lukacslacko/puzzle/438k.dxf

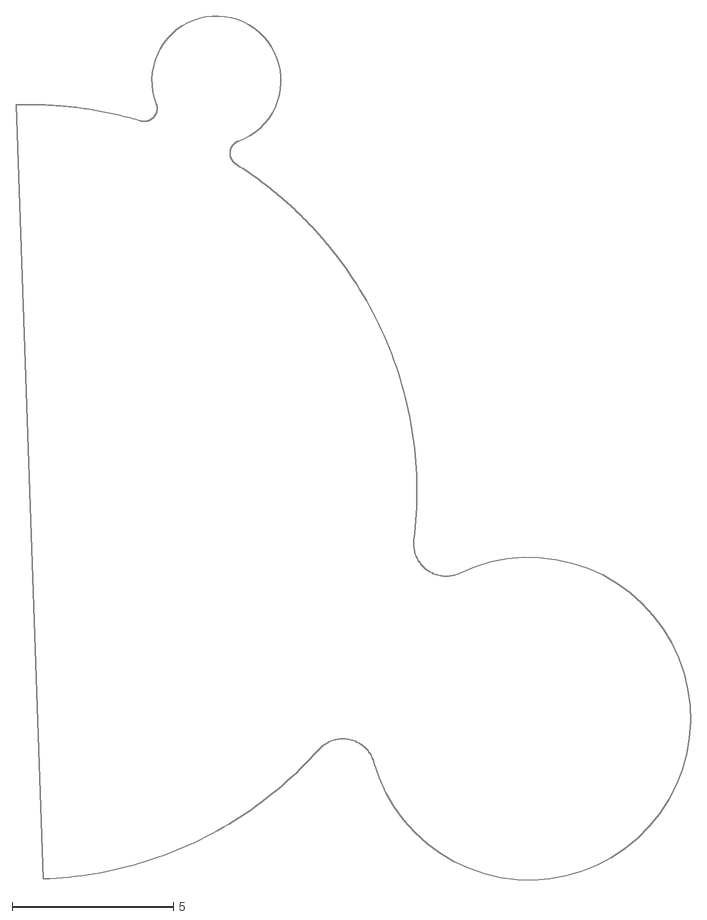
[picture p4: CAD file, 2023-12-27]
438k.dxf
20.9 x 26.8
