lukacslacko/puzzle/438l.dxf

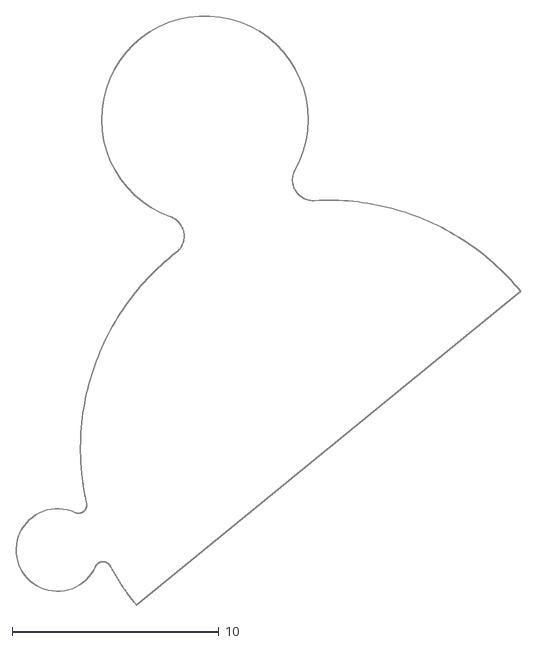
[picture p5: CAD file, 2023-12-27]
438l.dxf
24.4 x 28.5
