lukacslacko/puzzle/438c.dxf

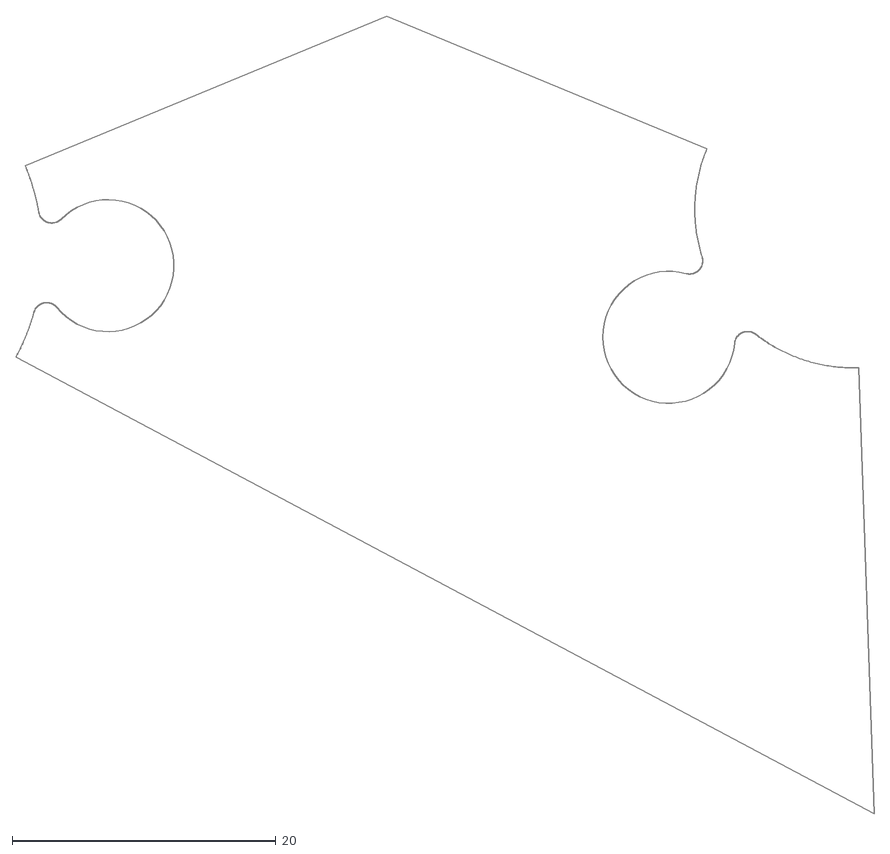
[picture p6: CAD file, 2023-12-27]
438c.dxf
65.0 x 60.4
