lukacslacko/puzzle/438j.dxf

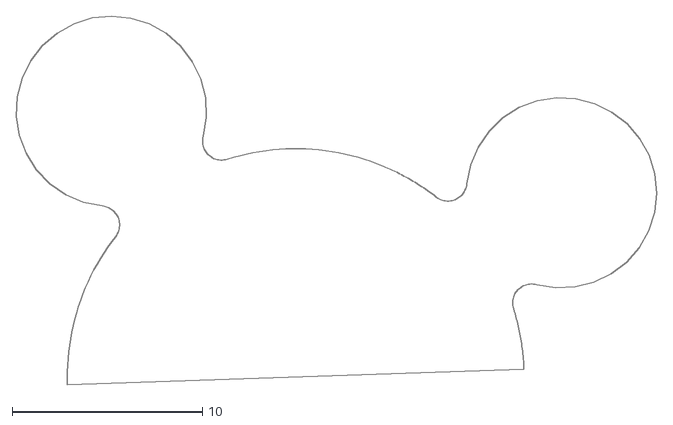
[picture p7: CAD file, 2023-12-27]
438j.dxf
33.6 x 19.4
