lukacslacko/puzzle/438m.dxf

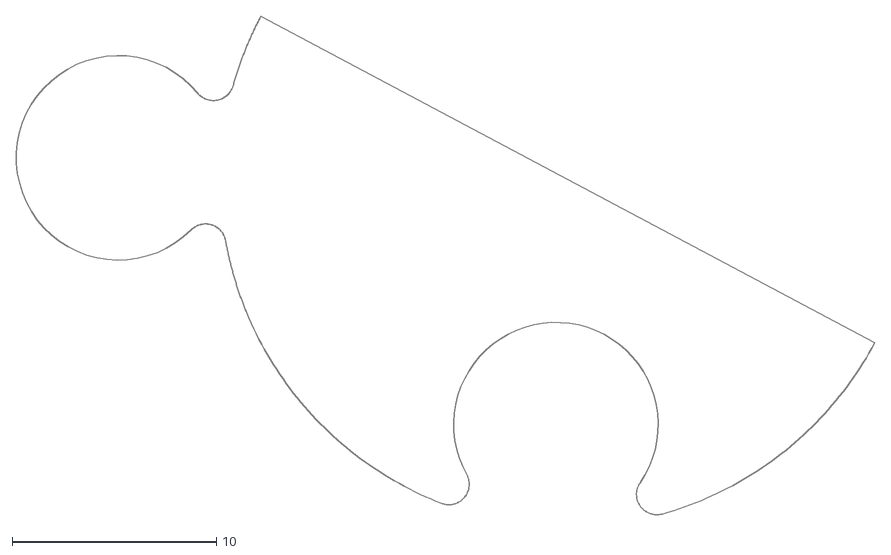
[picture p8: CAD file, 2023-12-27]
438m.dxf
42.0 x 24.4
