lukacslacko/puzzle/simple-sq-3-8-7.dxf

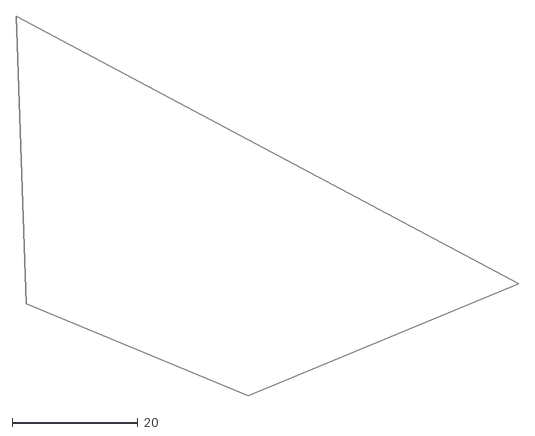
[picture p9: CAD file, 2023-12-27]
simple-sq-3-8-7.dxf
80.0 x 60.4
