lukacslacko/puzzle/simple-sq-3-8-3.dxf

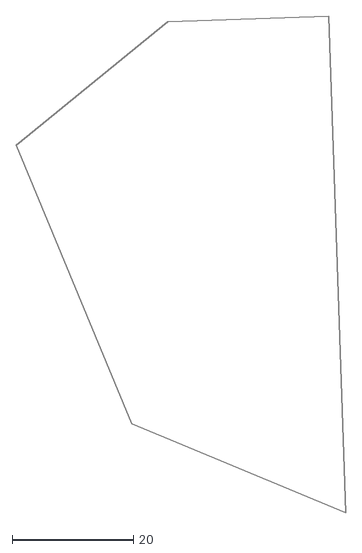
[picture p10: CAD file, 2023-12-27]
simple-sq-3-8-3.dxf
54.4 x 81.9
