lukacslacko/puzzle/simple-sq-3-8-1.dxf

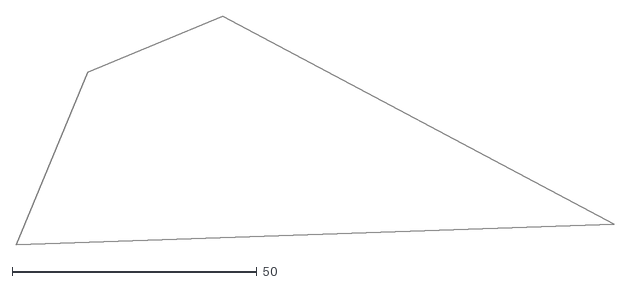
[picture p11: CAD file, 2023-12-27]
simple-sq-3-8-1.dxf
122.3 x 46.8
