lukacslacko/puzzle/438a.dxf

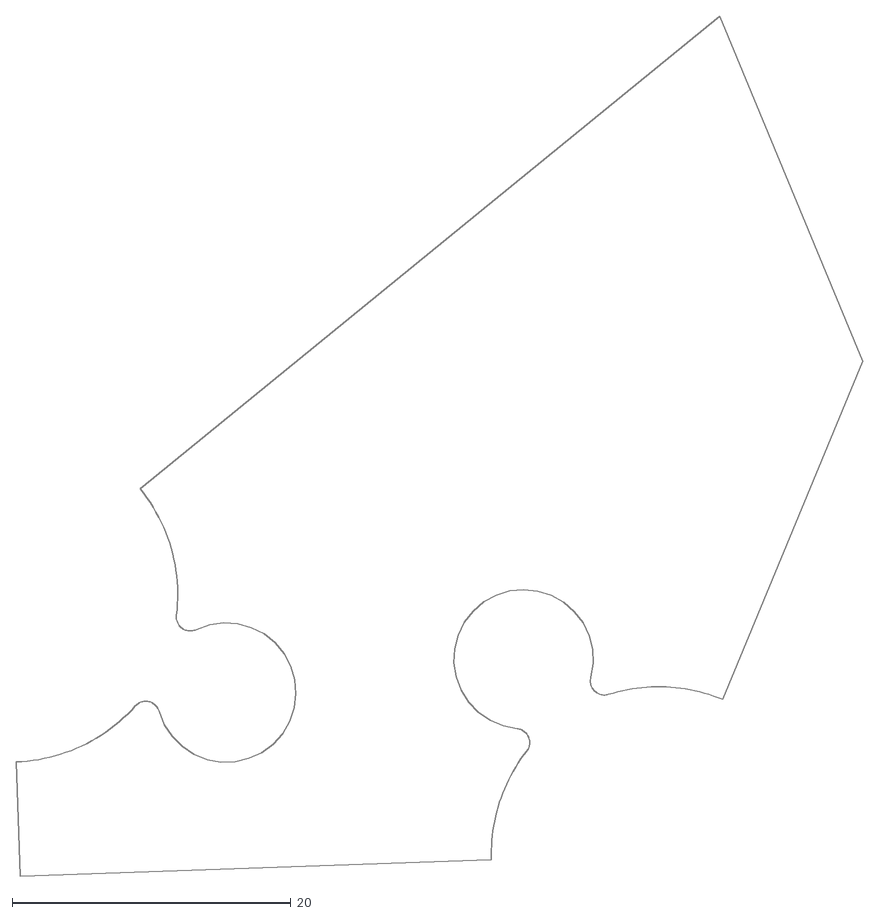
[picture p12: CAD file, 2023-12-27]
438a.dxf
60.7 x 61.7
