lukacslacko/puzzle/438d.dxf

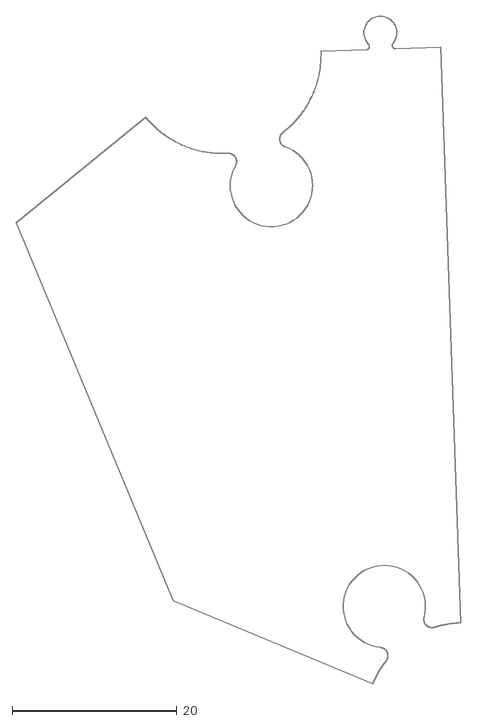
[picture p13: CAD file, 2023-12-27]
438d.dxf
54.0 x 81.1
