lukacslacko/puzzle/simple-sq-3-8-0.dxf

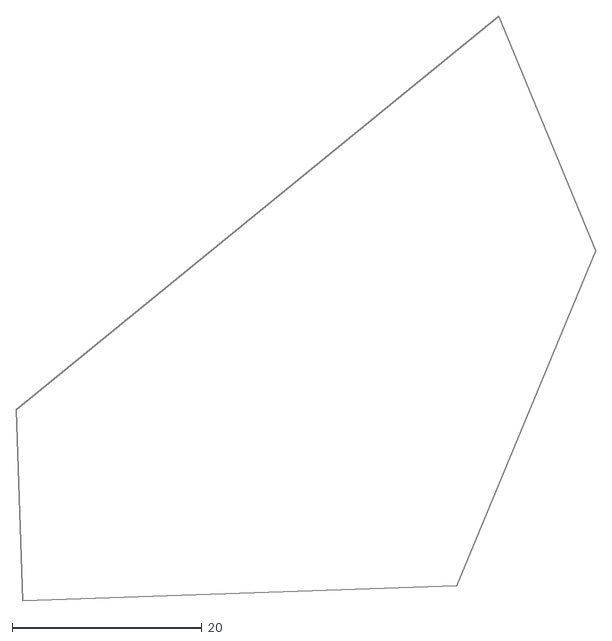
[picture p14: CAD file, 2023-12-27]
simple-sq-3-8-0.dxf
61.1 x 61.7
