lukacslacko/puzzle/438g.dxf

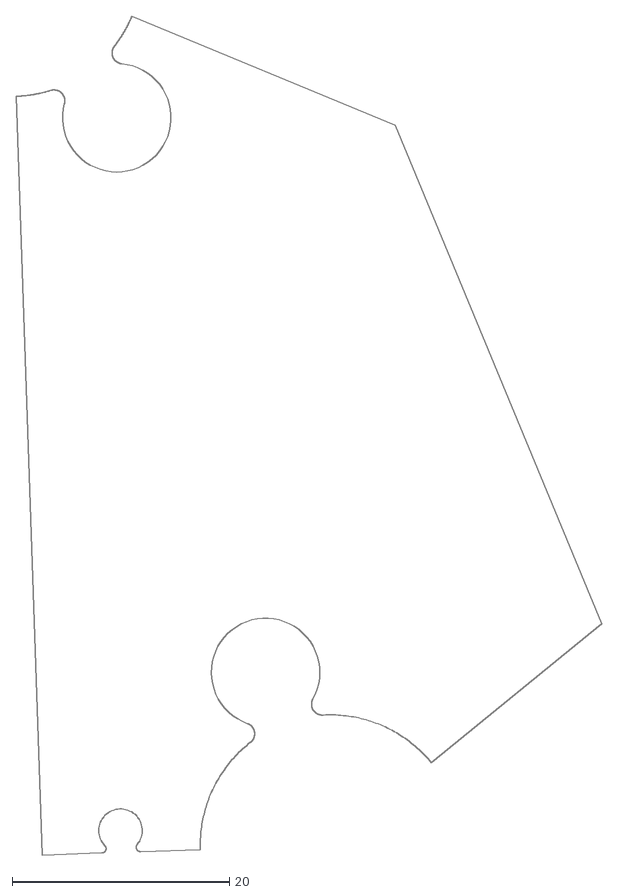
[picture p15: CAD file, 2023-12-27]
438g.dxf
54.0 x 77.3
