lukacslacko/puzzle/simple-sq-3-8-4.dxf

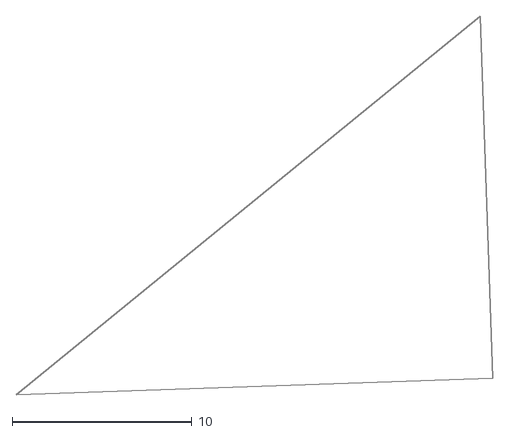
[picture p16: CAD file, 2023-12-27]
simple-sq-3-8-4.dxf
26.6 x 21.1
