lukacslacko/puzzle/438e.dxf

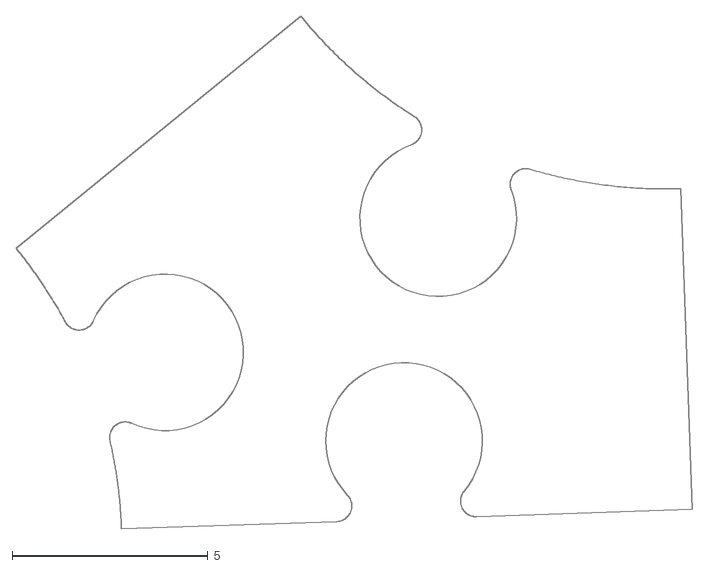
[picture p17: CAD file, 2023-12-27]
438e.dxf
17.3 x 13.1
