lukacslacko/puzzle/438i.dxf

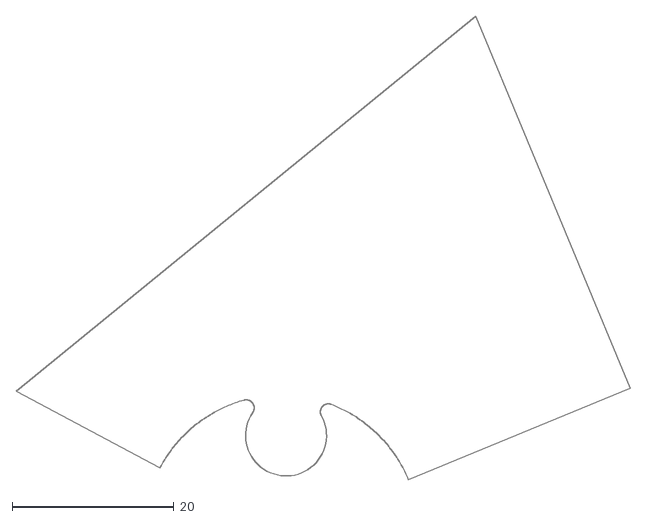
[picture p18: CAD file, 2023-12-27]
438i.dxf
75.9 x 57.3
