lukacslacko/puzzle/simple-sq-3-8-5.dxf

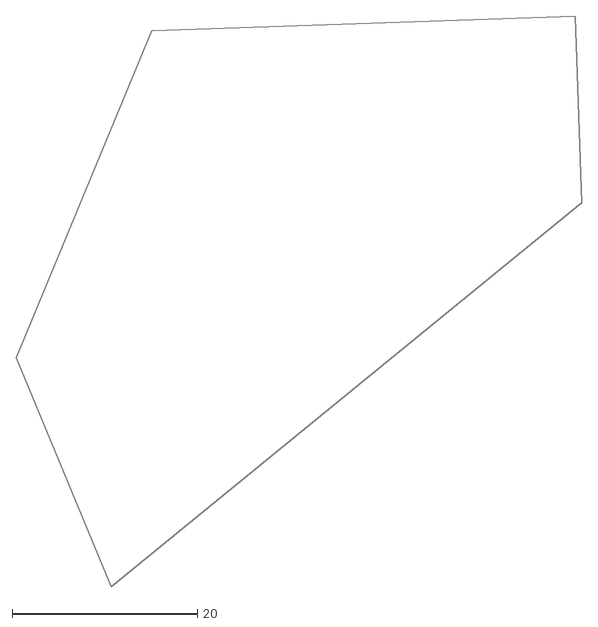
[picture p19: CAD file, 2023-12-27]
simple-sq-3-8-5.dxf
61.1 x 61.7
