lukacslacko/puzzle/simple-sq-3-8-9.dxf

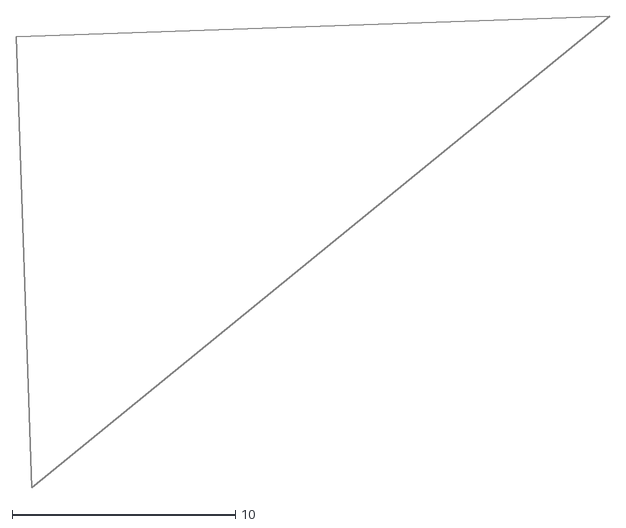
[picture p20: CAD file, 2023-12-27]
simple-sq-3-8-9.dxf
26.6 x 21.1
