lukacslacko/puzzle/simple-sq-3-8-8.dxf

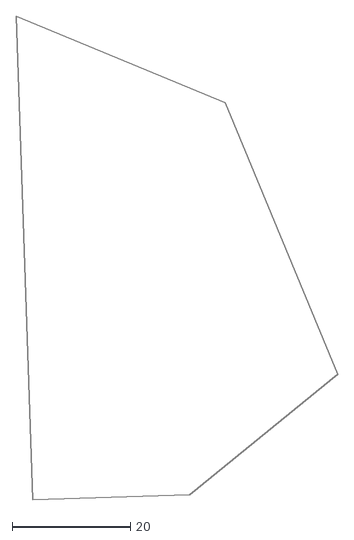
[picture p21: CAD file, 2023-12-27]
simple-sq-3-8-8.dxf
54.4 x 81.9
