lukacslacko/puzzle/simple-sq-3-8-12.dxf

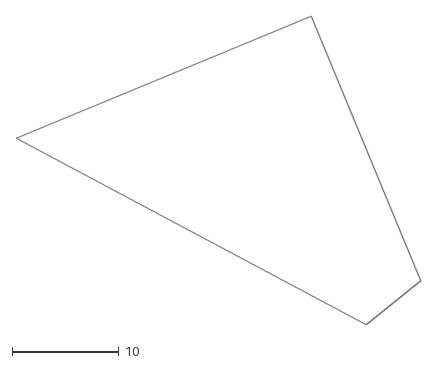
[picture p22: CAD file, 2023-12-27]
simple-sq-3-8-12.dxf
37.9 x 28.9
