lukacslacko/puzzle/simple-sq-3-8-11.dxf

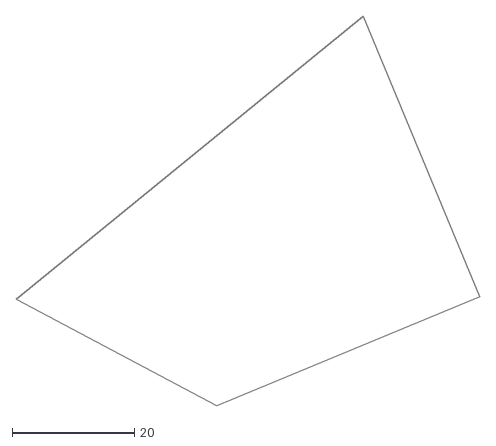
[picture p23: CAD file, 2023-12-27]
simple-sq-3-8-11.dxf
75.9 x 63.8
