lukacslacko/puzzle/simple-sq-3-8-13.dxf

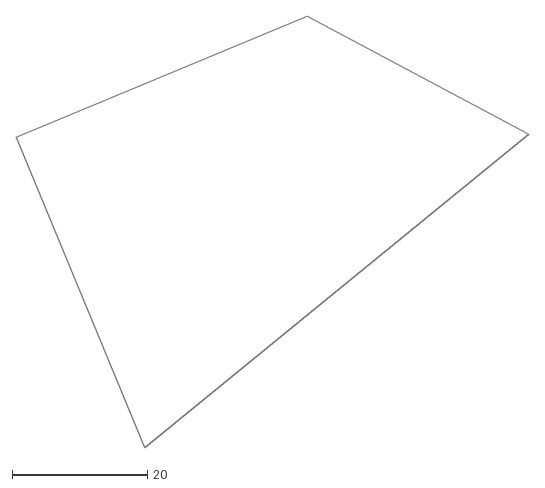
[picture p24: CAD file, 2023-12-27]
simple-sq-3-8-13.dxf
75.9 x 63.8
