lukacslacko/puzzle/simple-sq-3-8-6.dxf

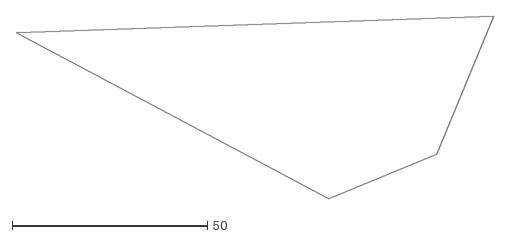
[picture p25: CAD file, 2023-12-27]
simple-sq-3-8-6.dxf
122.3 x 46.8
