lukacslacko/puzzle/simple-sq-3-8-2.dxf

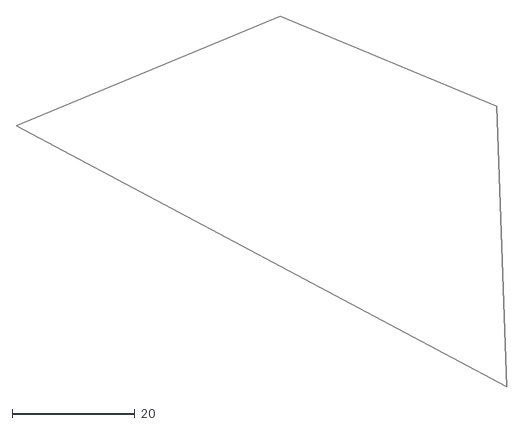
[picture p26: CAD file, 2023-12-27]
simple-sq-3-8-2.dxf
80.0 x 60.4
