lukacslacko/puzzle/438b.dxf

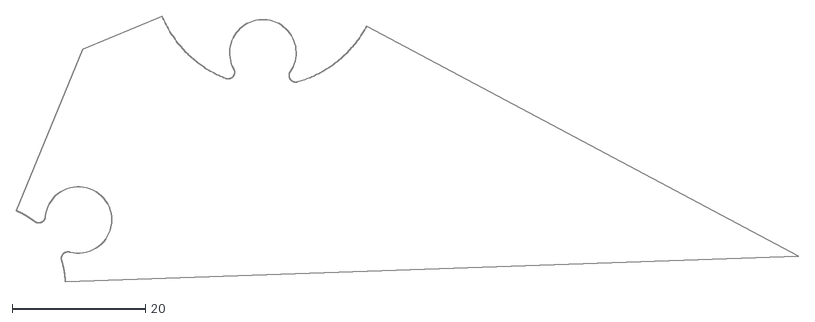
[picture p27: CAD file, 2023-12-27]
438b.dxf
117.7 x 39.9
