lukacslacko/puzzle/438f.dxf

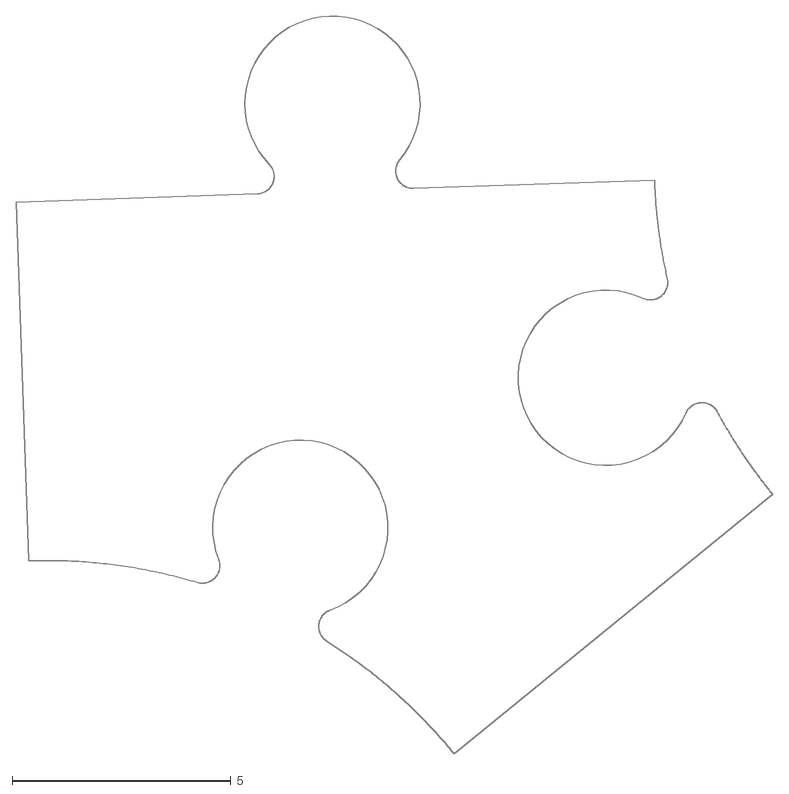
[picture p28: CAD file, 2023-12-27]
438f.dxf
17.3 x 16.8
