lukacslacko/puzzle/simple-sq-3-8-10.dxf

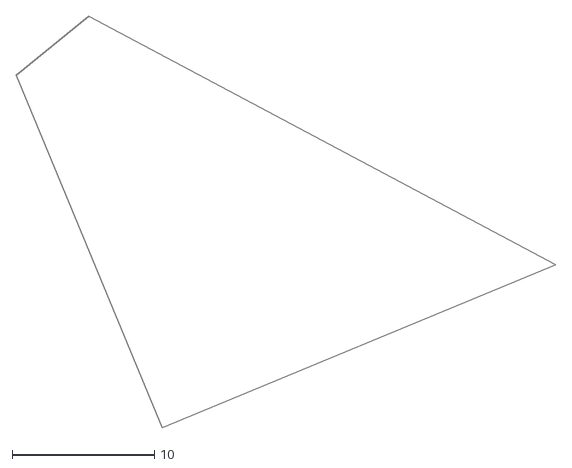
[picture p29: CAD file, 2023-12-27]
simple-sq-3-8-10.dxf
37.9 x 28.9
