lukacslacko/puzzle/438h.dxf

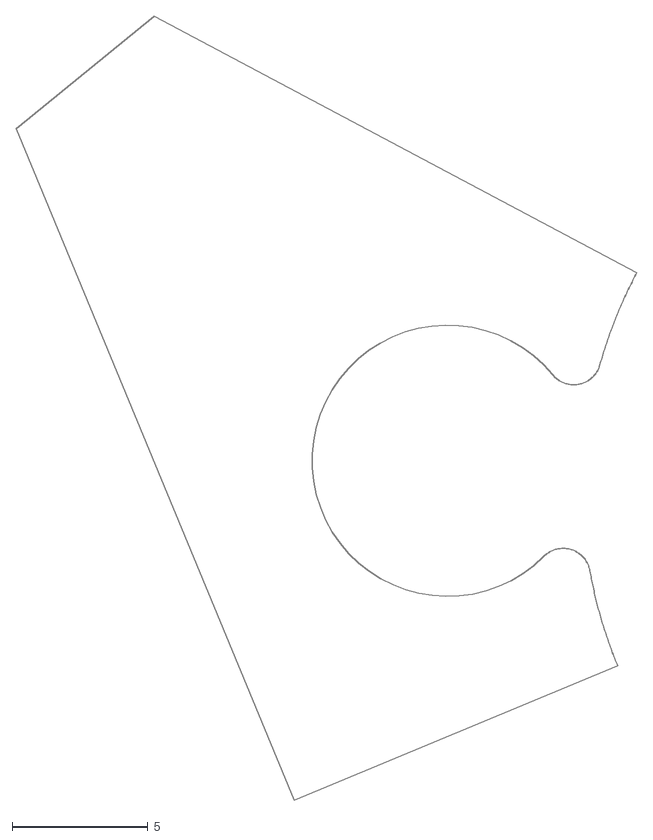
[picture p30: CAD file, 2023-12-27]
438h.dxf
22.9 x 28.9
