lukacslacko/puzzle/sq-3-8-a.dxf

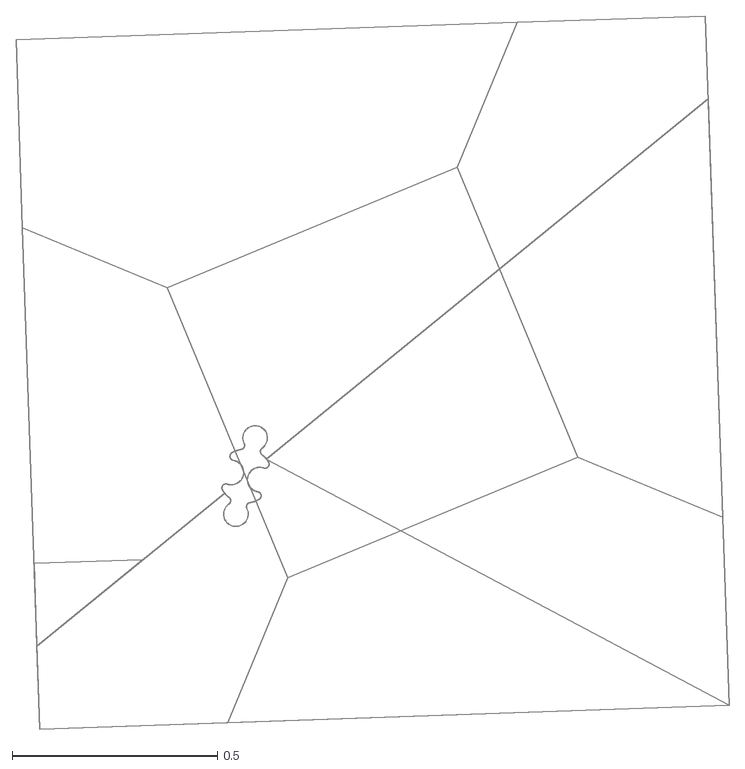
[picture p31: CAD file, 2023-12-26]
sq-3-8-a.dxf
1.74 x 1.74
