lukacslacko/puzzle/sq-3-8-b.dxf

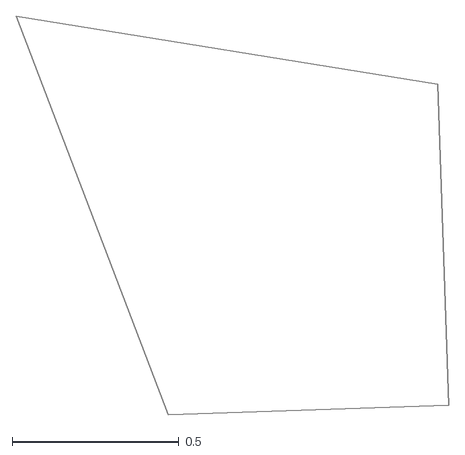
[picture p32: CAD file, 2023-12-26]
sq-3-8-b.dxf
1.29 x 1.19
