lukacslacko/puzzle/sq-tree-g.dxf

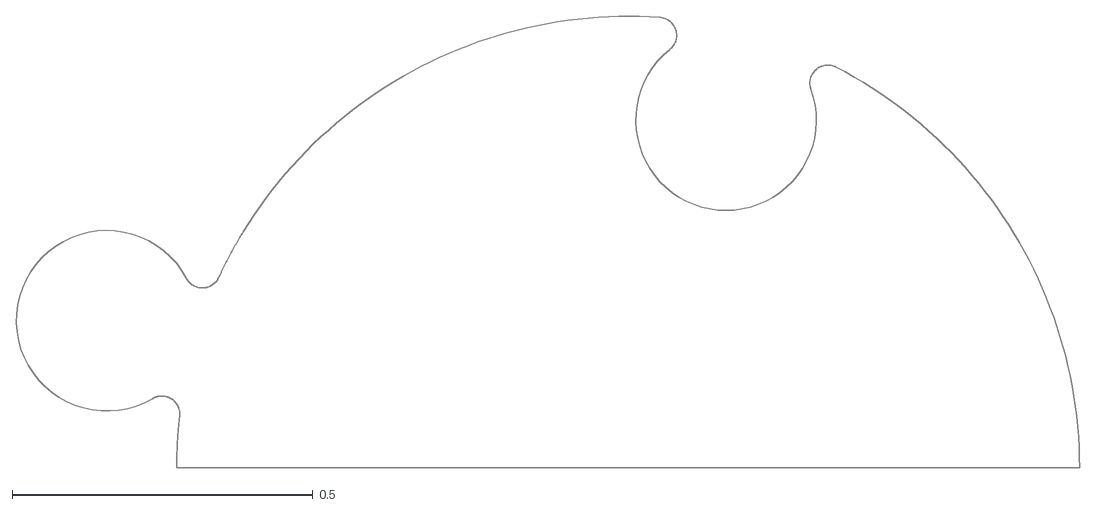
[picture p33: CAD file, 2023-12-25]
sq-tree-g.dxf
1.77 x 0.75
