lukacslacko/puzzle/sq-tree-b.dxf

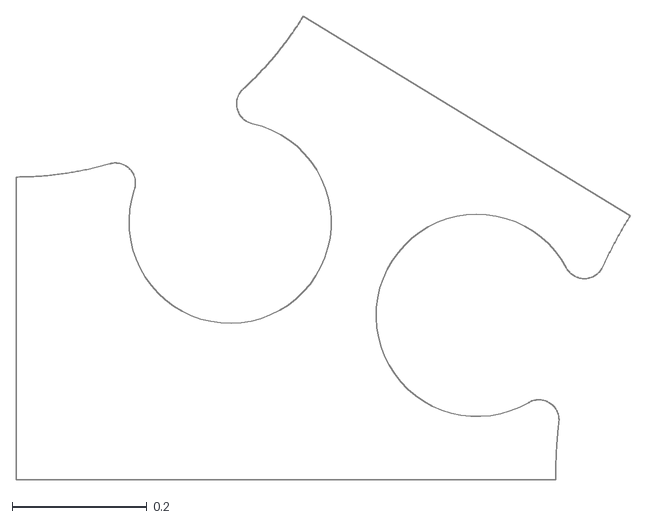
[picture p34: CAD file, 2023-12-25]
sq-tree-b.dxf
0.911 x 0.688
