lukacslacko/puzzle/sq-tree-d.dxf

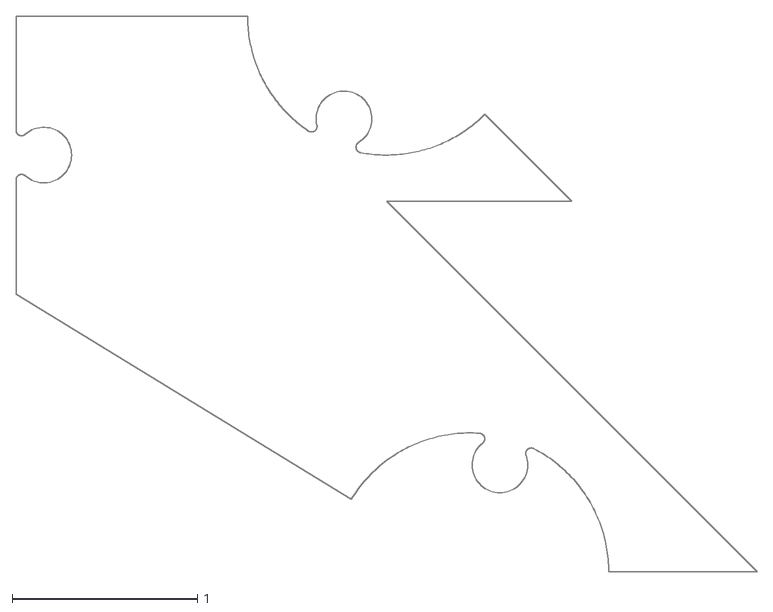
[picture p35: CAD file, 2023-12-25]
sq-tree-d.dxf
4.00 x 3.00
