lukacslacko/puzzle/sq-tree-f.dxf

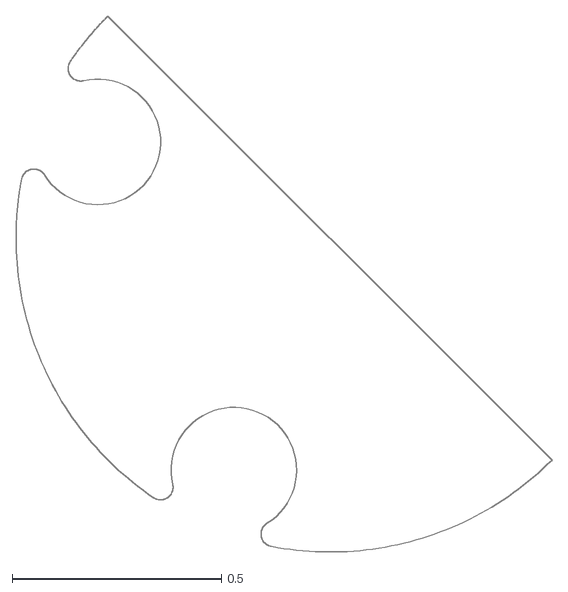
[picture p36: CAD file, 2023-12-25]
sq-tree-f.dxf
1.28 x 1.28
