lukacslacko/puzzle/linear_tab.dxf

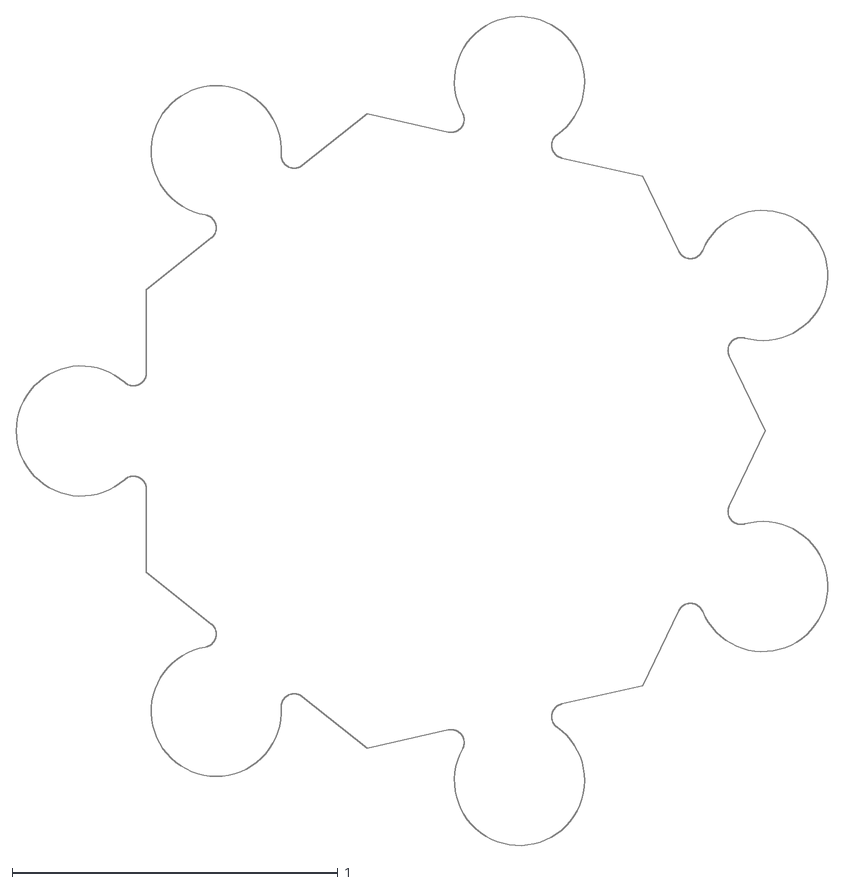
[picture p37: CAD file, 2023-12-25]
linear_tab.dxf
2.49 x 2.55
