lukacslacko/puzzle/sq-tree-a2.dxf

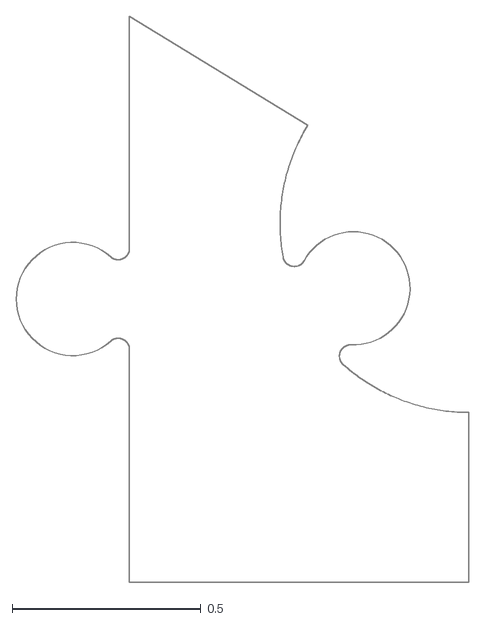
[picture p38: CAD file, 2023-12-25]
sq-tree-a2.dxf
1.20 x 1.50
