lukacslacko/puzzle/sq-tree-e.dxf

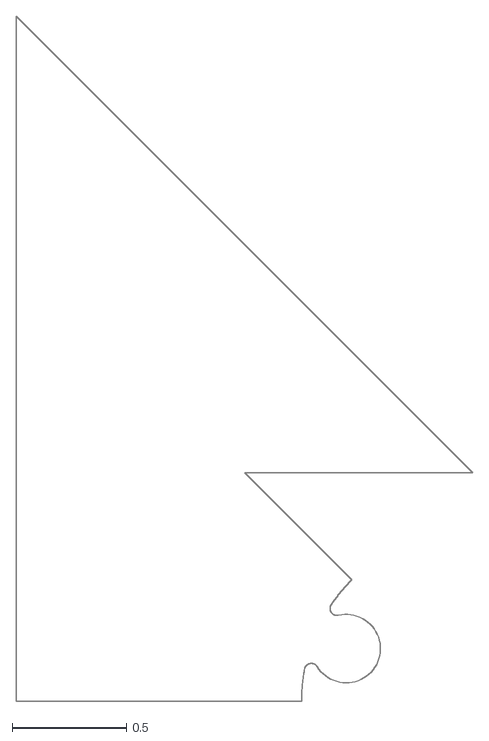
[picture p39: CAD file, 2023-12-25]
sq-tree-e.dxf
2.00 x 3.00
