lukacslacko/puzzle/sq-tree-a.dxf

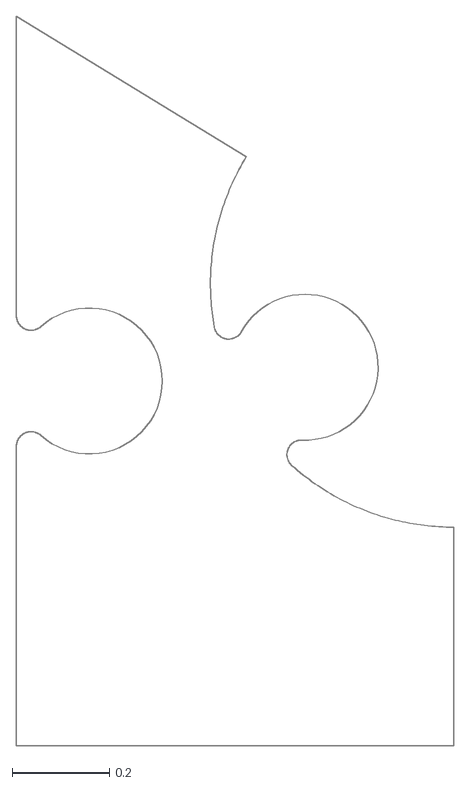
[picture p40: CAD file, 2023-12-25]
sq-tree-a.dxf
0.899 x 1.50
