lukacslacko/puzzle/sq-tree-c.dxf

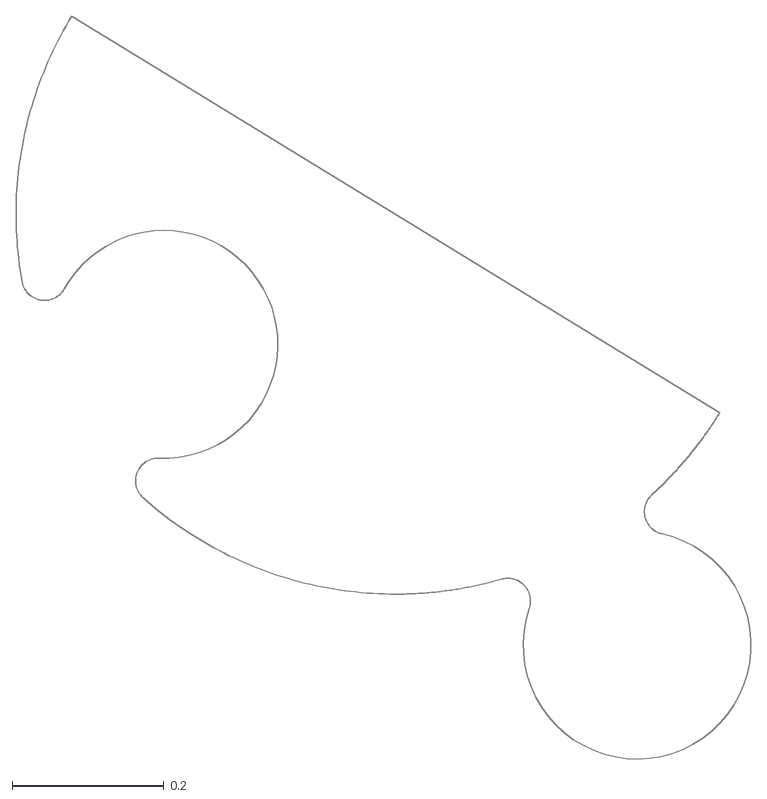
[picture p41: CAD file, 2023-12-25]
sq-tree-c.dxf
0.968 x 0.978
