lukacslacko/puzzle/sq-tree-d2.dxf

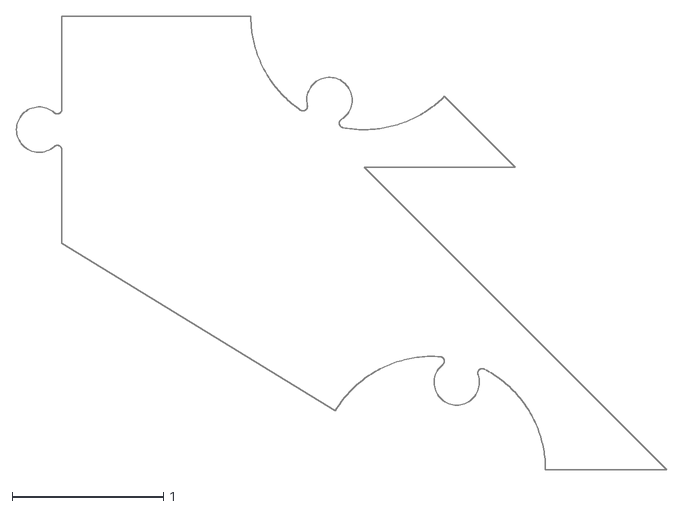
[picture p42: CAD file, 2023-12-25]
sq-tree-d2.dxf
4.30 x 3.00
