lukacslacko/puzzle/4--8-2-c.dxf

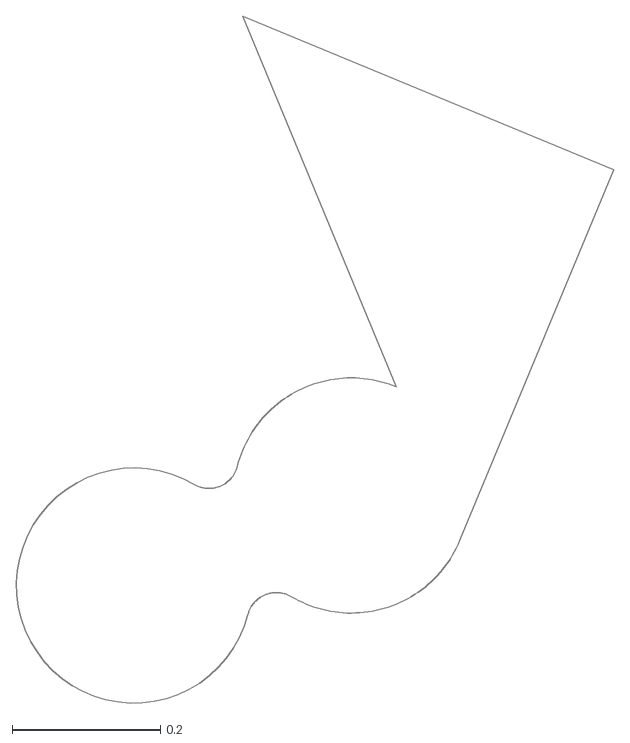
[picture p43: CAD file, 2023-12-24]
4--8-2-c.dxf
0.805 x 0.926
