lukacslacko/puzzle/sq-12-3-b.dxf

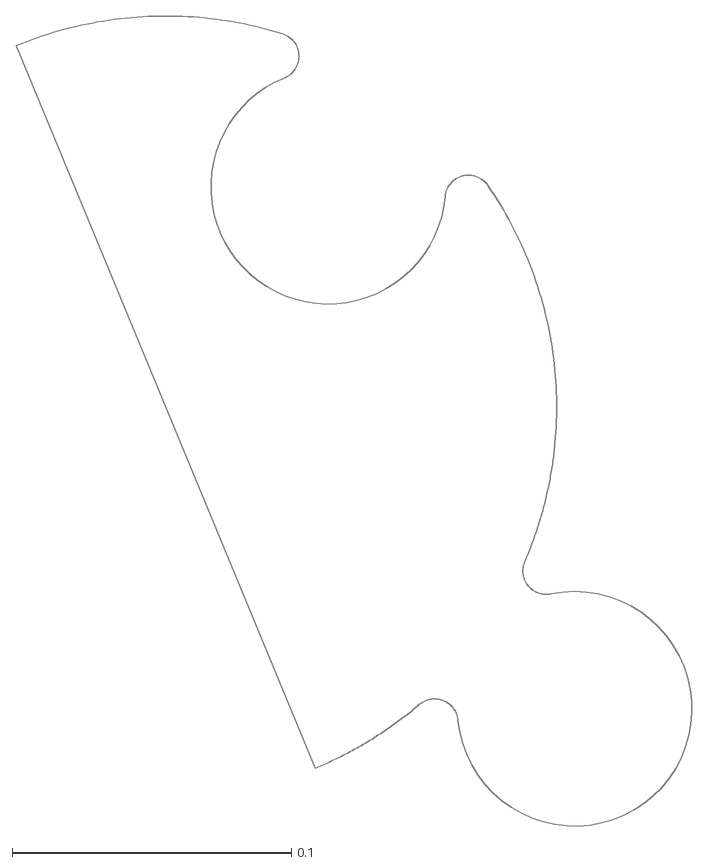
[picture p44: CAD file, 2023-12-24]
sq-12-3-b.dxf
0.242 x 0.29
