lukacslacko/puzzle/sq-12-3-a.dxf

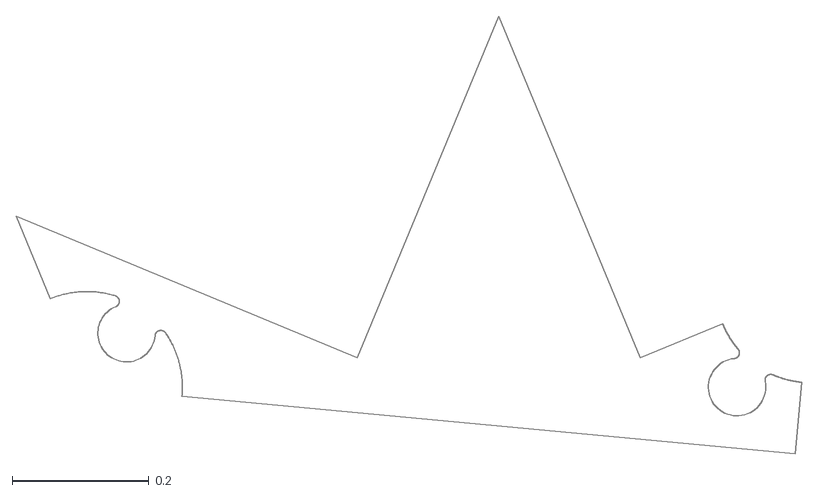
[picture p45: CAD file, 2023-12-24]
sq-12-3-a.dxf
1.15 x 0.64
