lukacslacko/puzzle/sq-12-3-d.dxf

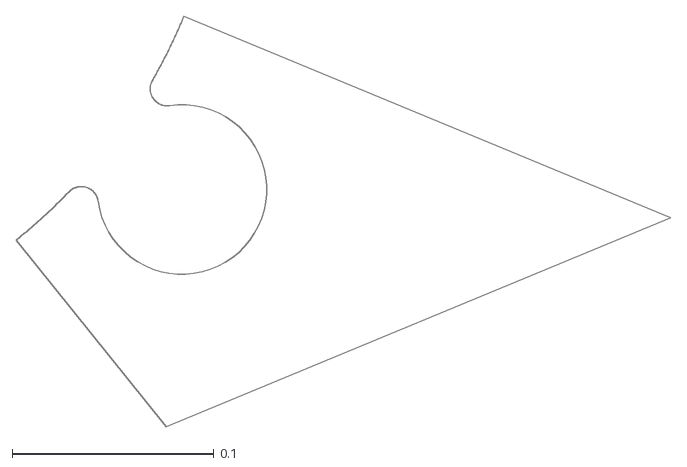
[picture p46: CAD file, 2023-12-24]
sq-12-3-d.dxf
0.324 x 0.204
