lukacslacko/puzzle/sq-12-3-c.dxf

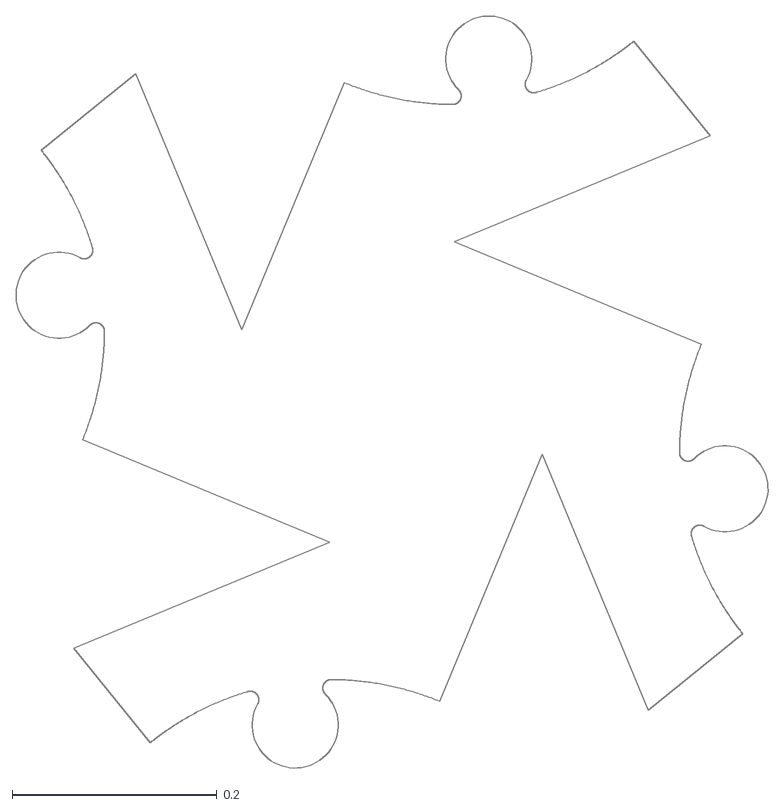
[picture p47: CAD file, 2023-12-24]
sq-12-3-c.dxf
0.734 x 0.734
