lukacslacko/puzzle/4--8-2-b.dxf

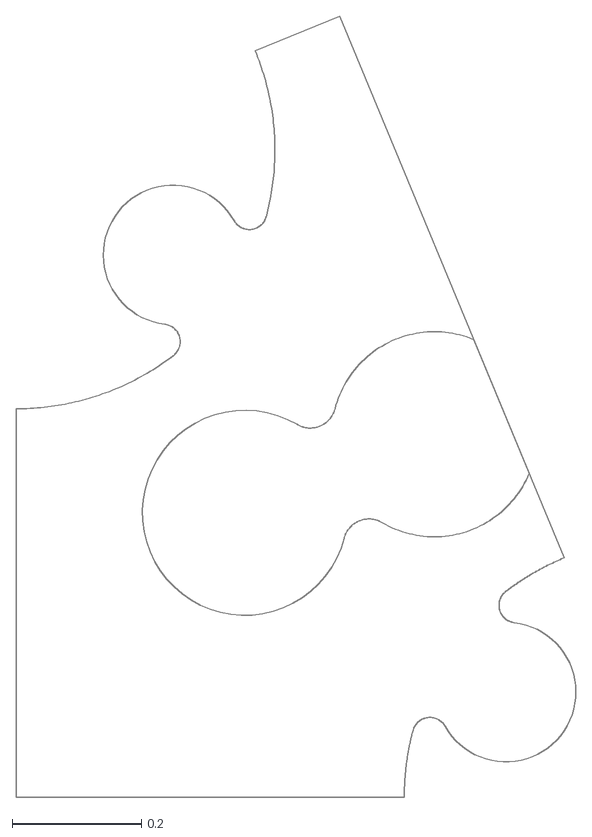
[picture p48: CAD file, 2023-12-24]
4--8-2-b.dxf
0.865 x 1.21
