lukacslacko/puzzle/sq-12-3-e.dxf

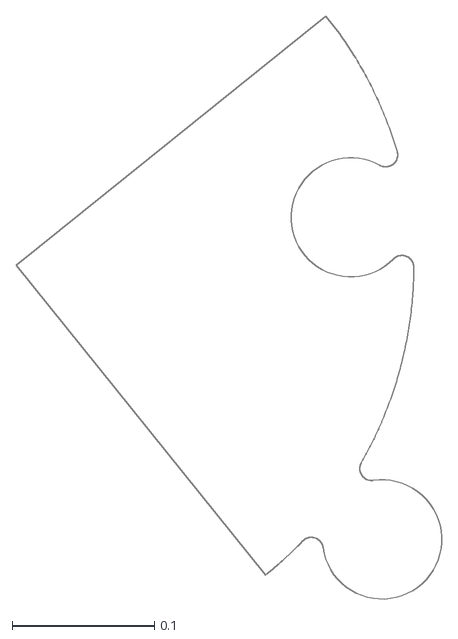
[picture p49: CAD file, 2023-12-24]
sq-12-3-e.dxf
0.3 x 0.411
