lukacslacko/puzzle/test2.dxf

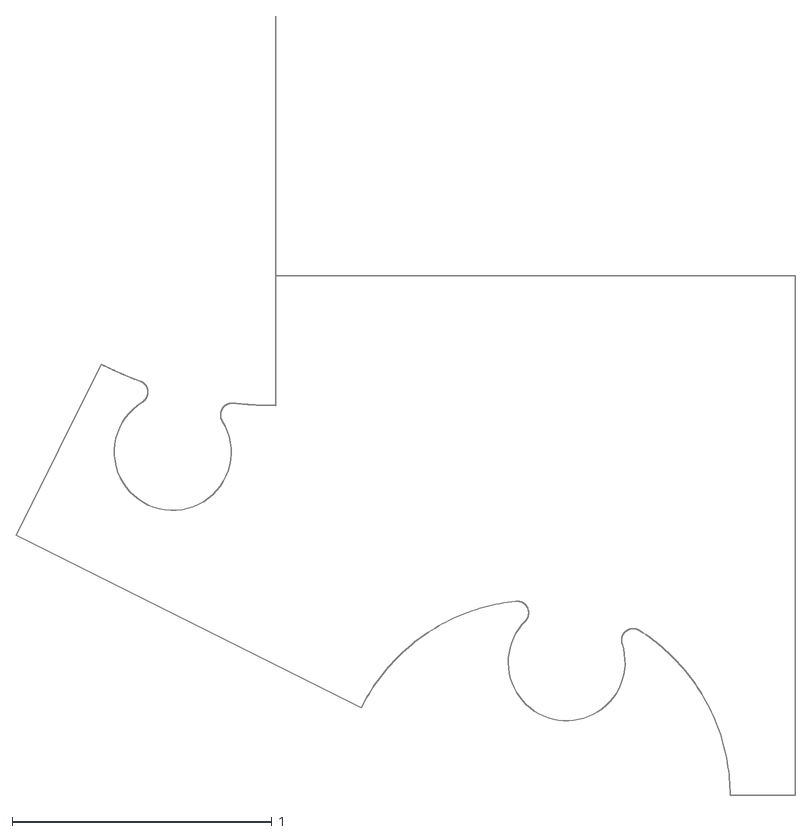
[picture p50: CAD file, 2023-12-22]
test2.dxf
3.00 x 3.00
