lukacslacko/puzzle/test.dxf

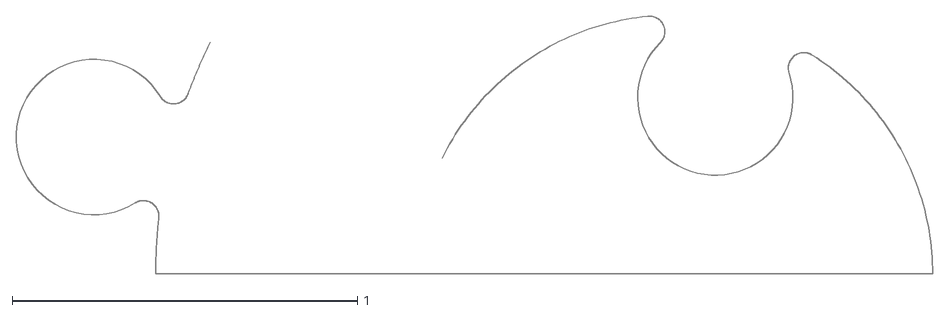
[picture p51: CAD file, 2023-12-22]
test.dxf
2.65 x 0.746
