lukacslacko/puzzle/4--8-2-a.dxf

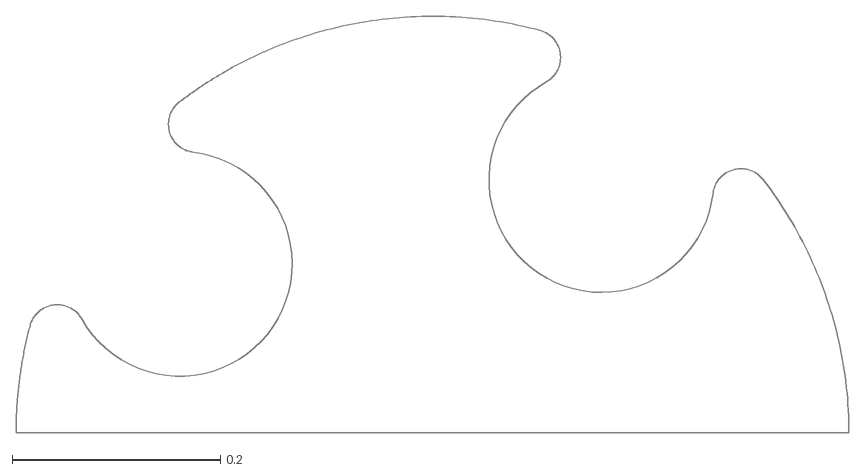
[picture p52: CAD file, 2023-12-22]
4--8-2-a.dxf
0.8 x 0.4
